javin-5/Guitar-Headphone-Amplifier/Simulation FIle/Simulation Circuit.asc

C1: cap; 220µ
C2: cap; 10µ
C3: cap; 33p
C4: cap; 10µ
D1: diode; 1N914
D2: diode; 1N914
Q1: npn; BC547C
Q2: pnp; BC557C
Q3: pnp; BC557C
Q4: npn; BC547C
R1: res; 0
R2: res; 2.2k
R3: res; 4.7k
R4: res; 100
R5: res; 10k
R6: res; 1
R7: res; 1
R8: res; 10k
R9: res; 100k
R10: res; 10k
U1: OP747
V1: voltage; SINE(0 0.01 100)
V2: voltage; 9V
V3: voltage; 9V
Named nets: Vcc, 0, Vee, Output, Input
.tran 0.09
